eltonlaw/avionics/fc2/fc2_board/fc2_board.kicad_sch

## KiCad design fc2/fc2_board/fc2_board.kicad_sch (2024-07-28, an earlier design)

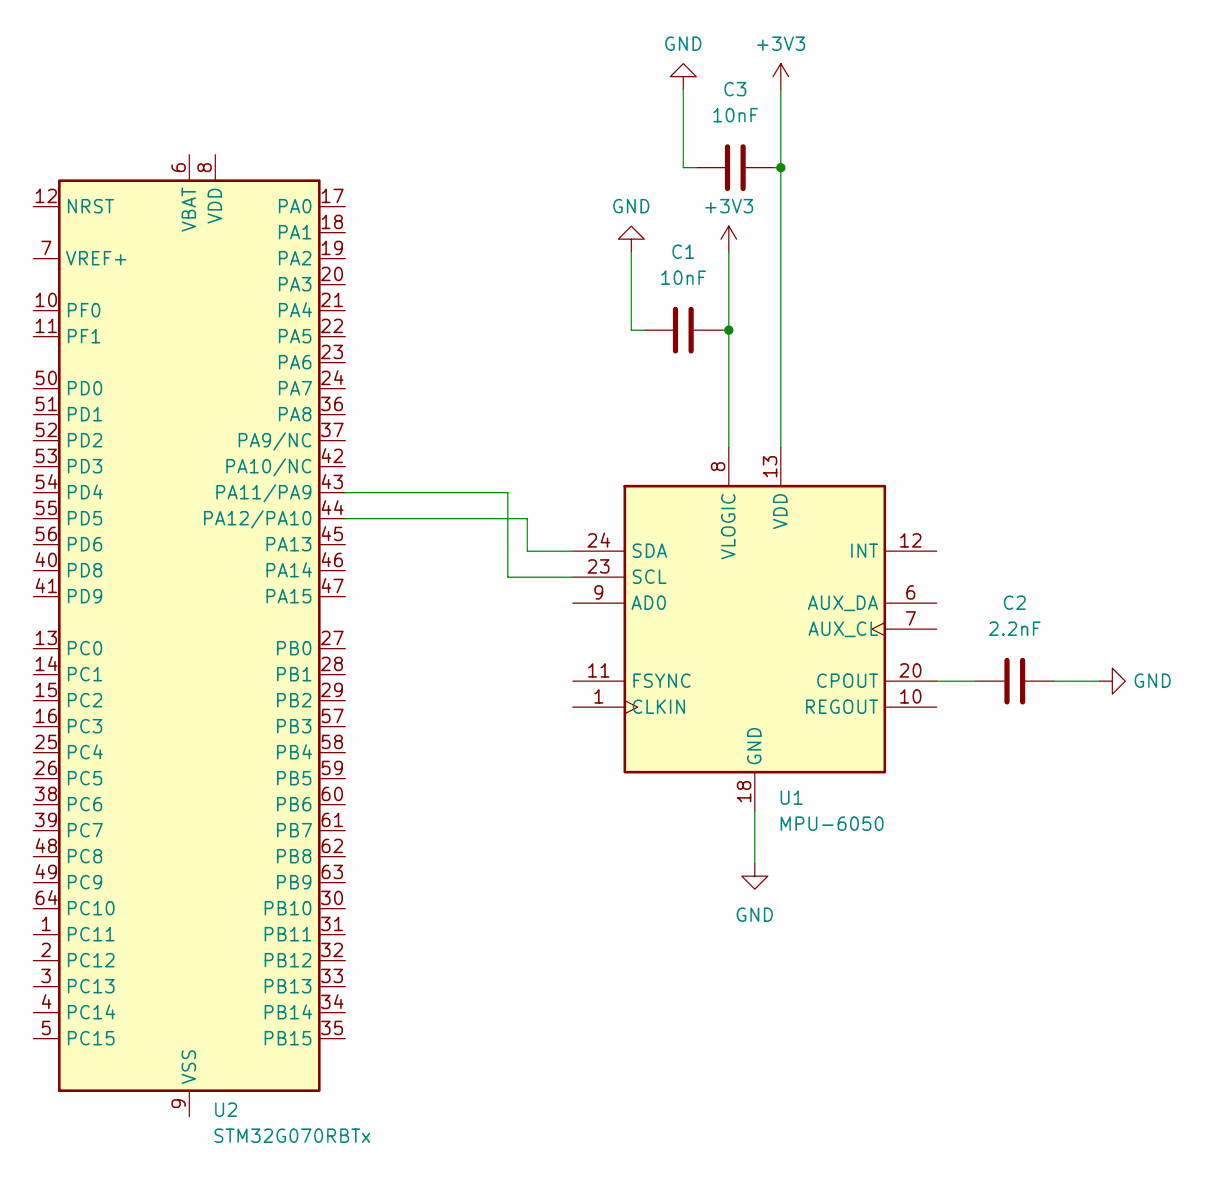
[picture p2: schematic fc2_board.kicad_sch]

Parts:
C1, C3: 10nF
C2: 2.2nF
U1: MPU-6050; InvenSense_QFN-24_4x4mm_P0.5mm
U2: STM32G070RBTx; LQFP-64_10x10mm_P0.5mm

Connections:
+3V3: C1.2, C3.2, U1.8 (VLOGIC), U1.13 (VDD)
GND: C1.1, C2.2, C3.1, U1.18 (GND)
unnamed: C2.1, U1.20 (CPOUT)
unnamed: U1.23 (SCL), U2.43 (PA11/PA9)
unnamed: U1.24 (SDA), U2.44 (PA12/PA10)
