eltonlaw/avionics/fc1/fc1board/fc1board.kicad_sch

## KiCad design fc1/fc1board/fc1board.kicad_sch (2023-08-12)

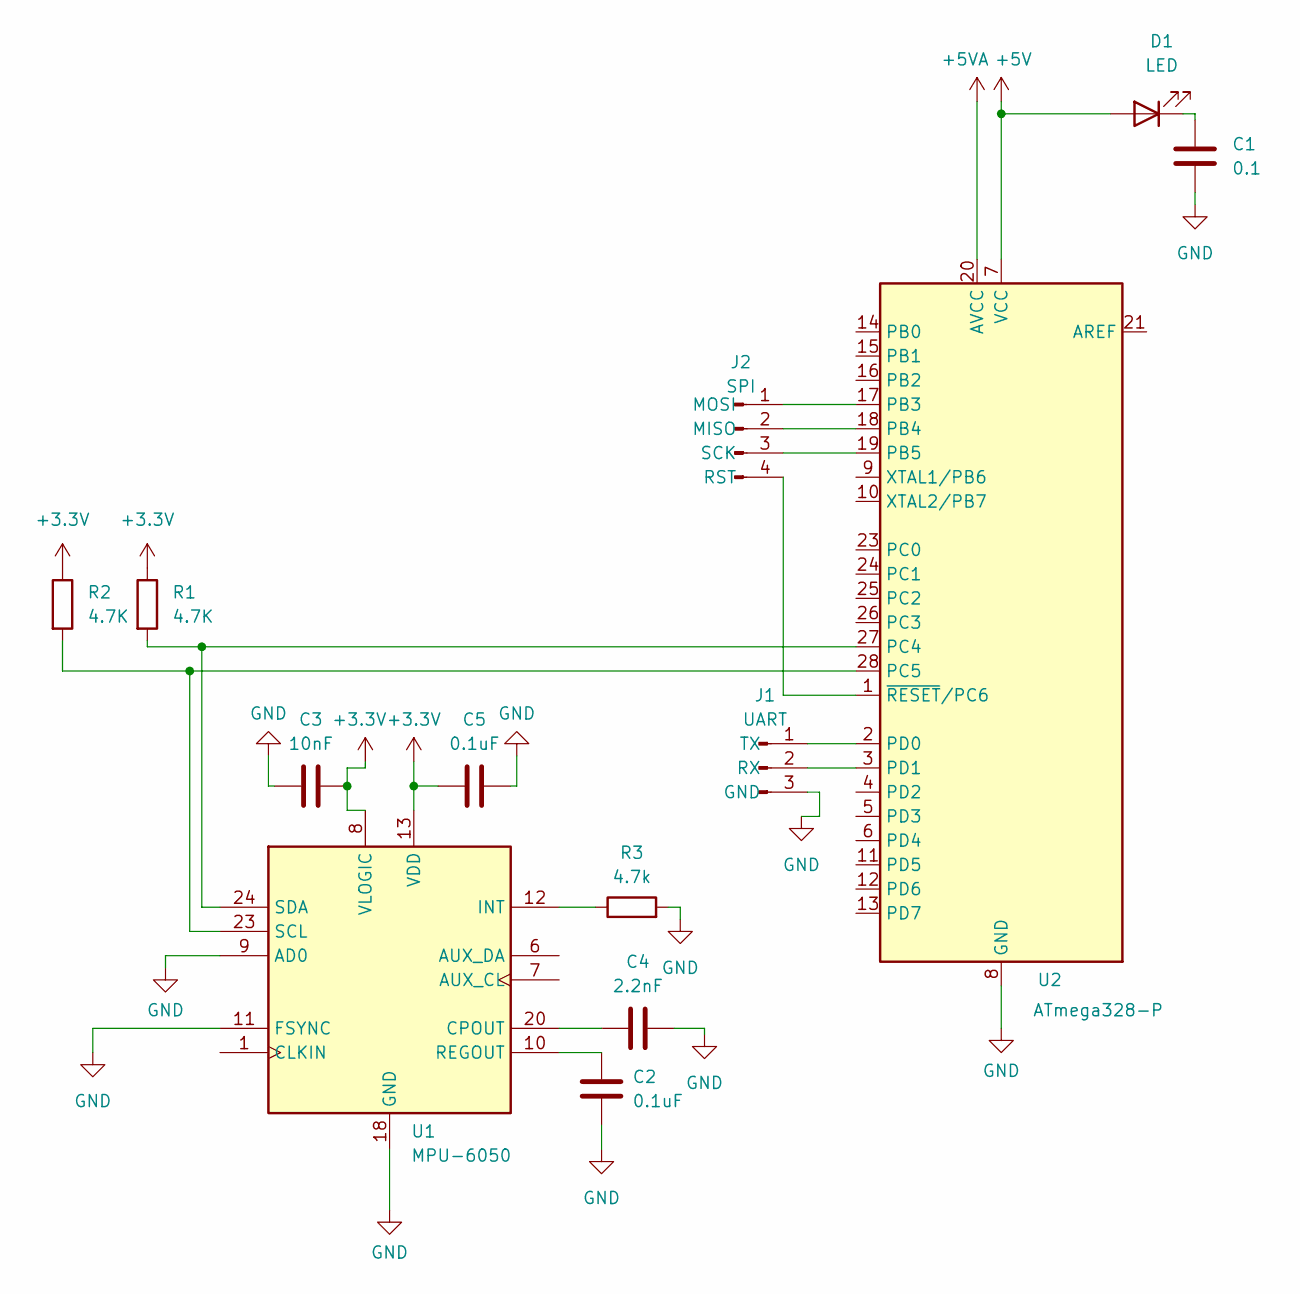
[picture p3: schematic fc1board.kicad_sch]

Parts:
C1: 0.1
C2, C5: 0.1uF
C3: 10nF
C4: 2.2nF
D1: LED
J1: UART
J2: SPI; JST_PH_B4B-PH-K_1x04_P2.00mm_Vertical
R1, R2: 4.7K
R3: 4.7k
U1: MPU-6050; InvenSense_QFN-24_4x4mm_P0.5mm
U2: ATmega328-P; DIP-28_W7.62mm

Connections:
+3.3V: C3.1, C5.1, R1.1, R2.1, U1.8 (VLOGIC), U1.13 (VDD)
+5V: D1.2 (A), U2.7 (VCC)
+5VA: U2.20 (AVCC)
GND: C1.2, C2.2, C3.2, C4.2, C5.2, J1.3 (GND), R3.2, U1.9 (AD0), U1.11 (FSYNC), U1.18 (GND), U2.8 (GND), U2.22 (GND)
unnamed: C1.1, D1.1 (K)
unnamed: C2.1, U1.10 (REGOUT)
unnamed: C4.1, U1.20 (CPOUT)
unnamed: J1.1 (TX), U2.2 (PD0)
unnamed: J1.2 (RX), U2.3 (PD1)
unnamed: J2.1 (MOSI), U2.17 (PB3)
unnamed: J2.2 (MISO), U2.18 (PB4)
unnamed: J2.3 (SCK), U2.19 (PB5)
unnamed: J2.4 (RST), U2.1 (~RESET/PC6)
unnamed: R1.2, U1.24 (SDA), U2.27 (PC4)
unnamed: R2.2, U1.23 (SCL), U2.28 (PC5)
unnamed: R3.1, U1.12 (INT)
