eltonlaw/avionics/avrlib/mpu6050.h

#pragma once

#include <util/twi.h>
#include "error.h"
#include "stm32g0xx_hal_i2c.h"

#define MPU6050_REG_SELF_TEST_X 0x0D
#define MPU6050_REG_SELF_TEST_Y 0x0E
#define MPU6050_REG_SELF_TEST_Z 0x0F
#define MPU6050_REG_SELF_TEST_A 0x10

#define MPU6050_REG_ACCEL_XOUT_H 0x3B
#define MPU6050_REG_ACCEL_XOUT_L 0x3C
#define MPU6050_REG_ACCEL_YOUT_H 0x3D
#define MPU6050_REG_ACCEL_YOUT_L 0x3E
#define MPU6050_REG_ACCEL_ZOUT_H 0x3f
#define MPU6050_REG_ACCEL_ZOUT_L 0x40
#define MPU6050_REG_TEMP_OUT_H   0x41
#define MPU6050_REG_TEMP_OUT_L   0x42
#define MPU6050_REG_GYRO_XOUT_H  0x43
#define MPU6050_REG_GYRO_XOUT_L  0x44
#define MPU6050_REG_GYRO_YOUT_H  0x45
#define MPU6050_REG_GYRO_YOUT_L  0x46
#define MPU6050_REG_GYRO_ZOUT_H  0x47
#define MPU6050_REG_GYRO_ZOUT_L  0x48

#define MPU6050_REG_PWR_MGMT 0x6B

#define MPU6050_REG_GYRO_CONFIG  0x1B
#define MPU6050_REG_ACCEL_CONFIG 0x1C

// Assumes AD0 = 0
#define MPU6050_I2C_SLA 0x68
// 7bit address + R/W bit
#define MPU6050_I2C_SLA_W (MPU6050_I2C_SLA << 1 | TW_WRITE)
#define MPU6050_I2C_SLA_R (MPU6050_I2C_SLA << 1 | TW_READ)

typedef enum {
    MPU6050_PWR_MGMT_OFF = 0,
} mpu6050_pwr_mgmt_t;

typedef enum {
    MPU6050_GYRO_RANGE_250 = 0,
    MPU6050_GYRO_RANGE_500,
    MPU6050_GYRO_RANGE_1000,
    MPU6050_GYRO_RANGE_2000,
} mpu6050_gyro_range_t;

typedef enum {
    MPU6050_ACCEL_RANGE_2 = 0,
    MPU6050_ACCEL_RANGE_4,
    MPU6050_ACCEL_RANGE_8,
    MPU6050_ACCEL_RANGE_16,
} mpu6050_accel_range_t;

typedef struct {
    int16_t accel_x;
    int16_t accel_y;
    int16_t accel_z;
    int16_t temp;
    int16_t gyro_x;
    int16_t gyro_y;
    int16_t gyro_z;
} mpu6050_reg_t;

typedef struct {
    mpu6050_reg_t* reg;
    float accel_scaler;
    float gyro_scaler;
} mpu6050_dev_t;

avcerr_t mpu6050_init(mpu6050_dev_t* mdev, mpu6050_gyro_range_t mgr, mpu6050_accel_range_t mar);
avcerr_t mpu6050_read(mpu6050_dev_t* mdev);
