eltonlaw/avionics/physics_sim/include/render.hpp

// System Headers
#define GLEW_STATIC
#include <stdio.h>
#include <GL/glew.h>
#include <GLFW/glfw3.h>

// Standard Headers
#include <cstdio>
#include <cstdlib>

namespace sim {

const int mWidth = 800;
const int mHeight = 600;

int render();

} // namespace sim
